peychart/WiFiPowerStrip/C++source/untyped.h

/*           untyped C++ (Version 0.1 - 2012/07)
    <https://github.com/peychart/untyped-cpp>

    Copyright (C) 2012  -  peychart

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
    Details of this licence are available online under:
                        http://www.gnu.org/licenses/gpl-3.0.html
*/
#ifndef HEADER_F2792F1A2356431
#define HEADER_F2792F1A2356431

#include <string>
#include <vector>
#include <map>
#include <iostream>
#include <sstream>
#include <cstdlib>

namespace noType
{
 class untyped : private std::vector<untyped>, private std::map<std::string, untyped>, private std::string
 {  static unsigned short JSON, tabSize;

 protected:
  typedef std::pair<std::string, untyped>  pairType;
  typedef std::vector<untyped>             vectorType;
  typedef std::map<std::string, untyped>   mapType;
  typedef unsigned char                    uchar;
  typedef long                             int64_t;
  typedef unsigned long                    uint64_t;

 public:
  inline static char const* version() {return "0.2";};
  untyped ( void );                   //  0
  untyped ( bool           const   ); //  1
  untyped ( char           const   ); //  2
  untyped ( wchar_t        const   ); //  3
  untyped ( int8_t         const   ); //  4
  untyped ( uint8_t        const   ); //  5
  untyped ( int16_t        const   ); //  6
  untyped ( uint16_t       const   ); //  7
  untyped ( int32_t        const   ); //  8
  untyped ( uint32_t       const   ); //  9
  untyped ( int64_t        const   ); // 10
  untyped ( uint64_t       const   ); // 11
  untyped ( float          const   ); // 12
  untyped ( double         const   ); // 13
  untyped ( char           const * ); // 15
  untyped ( std::string    const & ); // 15
  untyped ( size_t s, void const * ); // 15
  untyped ( pairType       const & ); //  0
  untyped ( vectorType     const & ); //  0
  untyped ( mapType        const & ); //  0
  untyped ( untyped        const & );
  untyped ( std::istream         & );
  virtual ~untyped() {clear();};

  inline size_t                       type        ( void )                const {return (size_t)_type;};
  inline size_t                       size        ( void )                const {return std::string::size();};
  inline size_t                       vectorSize  ( void )                const {return vectorType::size();};
  inline size_t                       mapSize     ( void )                const {return mapType::size();};
  inline bool                         empty       ( void )                const {return( !size() && !vectorSize() && !mapSize() );};

  inline untyped&                     clear       ( void )                      {return clearValue().clearMap().clearVector();};
  inline untyped&                     clearValue  ( void )                      {std::string::clear(); _type=0; return *this;};
  inline untyped&                     clearVector ( void )                      {vectorType::clear(); return *this;};
  inline untyped&                     clearMap    ( void )                      {mapType::clear();    return *this;};
  inline char const *                 data        ( void )                const {return std::string::data();};
  inline char const *                 c_str       ( void )                const {return std::string::c_str();};

  inline std::string&                 string      ( void )                      {return (*((std::string*)this));};
  inline vectorType&                  vector      ( void )                      {return (*((vectorType*)this));};
  inline untyped&                     at          ( size_t i )                  {return vectorType::at(i);};
  inline mapType&                     map         ( void )                      {return (*((mapType*)this));};
  inline untyped&                     at          ( const char s[] )            {return mapType::at(s);};
  inline untyped&                     at          ( std::string s )             {return mapType::at(s);};

  untyped&                            assign      ( untyped const &  );
  template<class T> untyped&          assign      ( T       const &v )          {return assign( untyped( v ) );};
  template<class T> untyped&          assign      ( char    const *v )          {return assign( untyped( v ) );};
  inline untyped&                     assign      ( size_t s, void const *v )   {return assign( untyped( s, v ) );};

  template<typename T> inline T       value       ( T &v )                const {return  v=this->value<T>();};
  template<typename T> inline T*      value       ( T* &p )               const {return  p=reinterpret_cast<T*>(data());};
  template<typename T> inline T const *value      ( T const * &p )        const {return  p=reinterpret_cast<T const *>(data());};
  template<typename T> T              value       ( void )                const {
    switch( _type ) {
      case  1: if( size() ) return( *reinterpret_cast<bool     const *>(data()) ); break;
      case  2: if( size() ) return( *reinterpret_cast<char     const *>(data()) ); break;
      case  3: if( size() ) return( *reinterpret_cast<wchar_t  const *>(data()) ); break;
      case  4: if( size() ) return( *reinterpret_cast<int8_t   const *>(data()) ); break;
      case  5: if( size() ) return( *reinterpret_cast<uint8_t  const *>(data()) ); break;
      case  6: if( size() ) return( *reinterpret_cast<int16_t  const *>(data()) ); break;
      case  7: if( size() ) return( *reinterpret_cast<uint16_t const *>(data()) ); break;
      case  8: if( size() ) return( *reinterpret_cast<int32_t  const *>(data()) ); break;
      case  9: if( size() ) return( *reinterpret_cast<uint32_t const *>(data()) ); break;
      case 10: if( size() ) return( *reinterpret_cast<int64_t  const *>(data()) ); break;
      case 11: if( size() ) return( *reinterpret_cast<uint64_t const *>(data()) ); break;
      case 12: if( size() ) return( *reinterpret_cast<float    const *>(data()) ); break;
      case 13: if( size() ) return( *reinterpret_cast<double   const *>(data()) ); break;
      case 15: return( *data() );
    } return T();
  };

  template<typename T>                operator T  ( void )               const  {return  value<T>();};
  template<typename T>                operator T* ( void )               const  {return  reinterpret_cast<T*>(data());};

  template<class T> untyped&          operator=   ( T const &that )             {return  operator= ( untyped( that ) );};
  inline untyped&                     operator=   ( untyped const &that )       {return  assign(that);};

  template<class T> bool              operator==  ( T const &that )       const {return  operator==( untyped( that ) );};
  bool                                operator==  ( untyped const &that ) const;
  template<class T> bool              operator!=  ( T const &that )       const {return  operator!=( untyped( that ) );};
  inline bool                         operator!=  ( untyped const &that ) const {return !operator==( that );};
  template<class T> bool              operator<   ( T const &that )       const {return  operator< ( untyped( that ) );};
  bool                                operator<   ( untyped const &that ) const;
  template<class T> bool              operator<=  ( T const &that )       const {return  operator<=( untyped( that ) );};
  inline bool                         operator<=  ( untyped const &that ) const {return( operator< ( that ) || operator==( that ) );};
  template<class T> bool              operator>   ( T const &that )       const {return  operator> ( untyped( that ) );};
  inline bool                         operator>   ( untyped const &that ) const {return !operator<=( that );};
  template<class T> bool              operator>=  ( T const &that )       const {return  operator>=( untyped( that ) );};
  inline bool                         operator>=  ( untyped const &that ) const {return !operator< ( that );};

  template<class T> inline untyped&   operator+=  ( T const &that )             {return  operator+=( untyped( that ) );};
  untyped&                            operator+=  ( untyped const & );
  template<class T> inline untyped    operator+   ( T const &that )       const {return  operator+ ( untyped( that ) );};
  inline untyped                      operator+   ( untyped const &that ) const {return  untyped( *this ).operator+=( that );};
  template<class T> inline untyped&   operator-=  ( T const &that )             {return  operator-=( untyped( that ) );};
  untyped&                            operator-=  ( untyped const &  );
  template<class T> inline untyped    operator-   ( T const &that )       const {return  operator- ( untyped( that ) );};
  inline untyped                      operator-   ( untyped const &that ) const {return  untyped( *this ).operator-=( that );};
  template<class T> inline untyped&   operator*=  ( T const &that )             {return  operator*=( untyped( that ) );};
  untyped&                            operator*=  ( untyped const &  );
  template<class T> inline untyped    operator*   ( T const &that )       const {return  operator* ( untyped( that ) );};
  inline untyped                      operator*   ( untyped const &that ) const {return  untyped( *this ).operator*=( that );};
  template<class T> inline untyped&   operator/=  ( T const &that )             {return  operator/=( untyped( that ) );};
  untyped&                            operator/=  ( untyped const &  );
  template<class T> inline untyped    operator/   ( T const &that )       const {return  operator/ ( untyped( that ) );};
  inline untyped                      operator/   ( untyped const &that ) const {return  untyped( *this ).operator/=( that );};
  template<class T> inline untyped&   operator%=  ( T const &that )             {return  operator%=( untyped( that ) );};
  untyped&                            operator%=  ( untyped const &  );
  template<class T> inline untyped    operator%   ( T const &that )       const {return  operator% ( untyped( that ) );};
  inline untyped                      operator%   ( untyped const &that ) const {return  untyped( *this ).operator%=( that );};
  template<class T> inline untyped&   operator&=  ( T const &that )             {return  operator&=( untyped( that ) );};
  untyped&                            operator&=  ( untyped const &  );
  template<class T> inline untyped    operator&   ( T const &that )       const {return  operator& ( untyped( that ) );};
  inline untyped                      operator&   ( untyped const &that ) const {return  untyped( *this ).operator&=( that );};
  template<class T> inline untyped&   operator|=  ( T const &that )             {return  operator|=( untyped( that ) );};
  untyped&                            operator|=  ( untyped const &  );
  template<class T> inline untyped    operator|   ( T const &that )       const {return  operator| ( untyped( that ) );};
  inline untyped                      operator|   ( untyped const &that ) const {return  untyped( *this ).operator|=( that );};

  inline untyped&                     operator[]  ( int n )                     {return operator[](size_t(n));};
  inline untyped&                     operator[]  ( long   n )                  {return operator[](size_t(n));};
  inline untyped&                     operator[]  ( size_t n )                  {while(n >= vectorSize()) vectorType::push_back(untyped()); return at(n);};
  inline untyped&                     operator[]  ( const char s[] )            {return( operator[]( std::string(s) ) );};
  inline untyped&                     operator[]  ( std::string s )             {mapType::iterator it(mapType::find(s)); return( (it!=mapType::end()) ?(it->second) :(mapType::operator[](s)=untyped()) );};

  virtual untyped&                    serialize       ( std::ostream & );
  virtual untyped&                    serializeJson   ( std::ostream &o )       {return serializePrettyJson( o, untyped::tabSize );};
  virtual untyped&                    serializePrettyJson( std::ostream &o, unsigned short v=1 )
                                                                                {unsigned short b(untyped::JSON),t(untyped::tabSize); prettyJson(v); o << *this; if((untyped::JSON=b)) prettyJson(t); return *this;};
  inline std::string                  serializeJson   ( void )                  {std::stringstream o; serializePrettyJson( o, untyped::tabSize ); return o.str();};
  inline std::string                  serializePrettyJson( unsigned short v=1 ) {std::stringstream o; serializePrettyJson( o, v );                return o.str();};

  virtual untyped&                    deserialize     ( std::string  s )        {std::istringstream i(s); return(isBinary() ?deserialize(i) :deserializeJson(i));};
  virtual untyped&                    deserialize     ( std::istream & );
  virtual untyped&                    deserializeJson ( std::string  s )        {std::istringstream i(s); return deserializeJson(i);};
  virtual untyped&                    deserializeJson ( std::istream & );
  inline untyped&                     operator()      ( std::string  s )        {std::istringstream i(s); return operator()(i);};
  inline untyped&                     operator()      ( std::istream &i )       {return deserialize(i);};

  friend std::ostream&                operator<<      ( std::ostream &, untyped const & );
  friend std::ostream&                operator<<      ( std::ostream &, mapType const & );
  friend std::ostream&                operator<<      ( std::ostream &, vectorType const & );
  friend std::ostream&                operator<<      ( std::ostream &out, pairType const &that ) {return out << that.first << ": " << that.second;};

  inline bool                         isBinary        ( void )            const {return( !untyped::JSON );};
  inline bool                         isJson          ( void )            const {return(  untyped::JSON );};
  inline bool                         isPrettyJson    ( void )            const {return(  untyped::tabSize );};
  inline untyped&                     binary          ( void )                  {untyped::JSON=untyped::tabSize=0; return *this;};
  inline untyped&                     json            ( void )                  {return prettyJson(0);};
  inline untyped&                     prettyJson      ( short v=1 )             {untyped::JSON=1; untyped::tabSize=(v<0 ?0 :v); return *this;};

 protected:
  static bool                         isNetFormat     ( void )                  {short isNotNet=1; return( !*reinterpret_cast<char const *>(&isNotNet) );};
  template<typename T> static char const *hton        ( T val )                 {
    static T tmp; tmp=val; ntoh( reinterpret_cast<char*>(&tmp), sizeof(T) );
    return( reinterpret_cast<char const *>(&tmp) );
  };  // Net to Host format...
  inline void                         ntoh            ( std::string& p )        {
    if (p.size() && !isNetFormat() )
      for(size_t i(0), j(p.size()-1); i<j; i++, j--)
        std::swap( p[i], p[j] );
  };
  template<typename T> static inline void ntoh        ( T *p, size_t const size ){
    if (p && !isNetFormat())
      for( char *pt1=reinterpret_cast<char*>(p),*pt2 = pt1+size-1; pt1<pt2; pt1++,pt2-- )
        std::swap( *pt1, *pt2 );
  };

  static inline size_t        stringSize      ( char const *v )                 {size_t s(0); if (v) while( *v++ ) s++; return s;};

 private:
  uchar                       _type; /// WARNING: type must be < 32 [5+3 bits shared with desc(structure) in a char for the serialization methods...]

  inline void                 _set            ( size_t l,char const* v )        {std::string::assign(v, l);};
  inline void                 _set            ( vectorType   const &v )         {for(size_t i(0); i<v.size(); i++) operator[](vectorSize())= v[i];};
  inline void                 _set            ( mapType      const &v )         {for(mapType::const_iterator it=v.begin(); it!=v.end(); it++) operator[](it->first)= it->second;};
  static void                 _writeTypeAndStructure( std::ostream&, uchar, uchar const & );
  static inline void          _writeSize      ( std::ostream& o, size_t s )     {o.write( hton(s), sizeof(s) );};
  static uchar                _readTypeAndStructure ( std::istream&, uchar & );
  static inline void          _readSize       ( std::istream &in, size_t &s )   {if( in.read(reinterpret_cast<char*>(&s), sizeof(s)) ) ntoh( &s, sizeof(s) );};

  static untyped              _getJsonObject  ( std::istream &, char &, bool=false );
  static untyped              _getJsonArray   ( std::istream &, char &, bool=false );
  static untyped              _getJsonValue   ( std::istream &, char &, char='\0' );
  static untyped              _getJsonString  ( std::istream &, char & );
  static untyped              _getJsonChar    ( std::istream &, char & );
  static untyped              _getJsonNumber  ( std::istream &, char & );
  static untyped              _getJsonBool    ( std::istream &, char & );
  static void                 _getJsonNull    ( std::istream &, char & );
  static void                 _getJsonComment ( std::istream &, char & );
  static inline void          _jsonTAB        ( std::ostream &o )               {if(untyped::JSON) for(unsigned short i(untyped::JSON-1); i; i--) o.write(" ", 1);};
  static inline void          _jsonNL         ( std::ostream &o )               {if(untyped::tabSize) o.write("\n", 1);};
  static inline void          _jsonSP         ( std::ostream &o )               {if(untyped::tabSize) o.write(" ", 1);};
  static inline void          _jsonINCR       ( void )                          {if(untyped::JSON) untyped::JSON+=untyped::tabSize;};
  static inline void          _jsonDECR       ( void )                          {if(untyped::JSON>untyped::tabSize) untyped::JSON-=untyped::tabSize;};

  static inline bool          _isWhiteSpace   ( char &c )                       {if(c==' ' || c=='\t' || c=='\r' || c=='\n') return true; return false;};
 };
}
using namespace noType;
#endif
