peychart/WiFiPowerStrip/C++source/mqtt.h

/* ESP8266-MQTT-Manager C++ (Version 0.1 - 2020/07)
    <https://github.com/peychart/WiFiPowerStrip>

    Copyright (C) 2020  -  peychart

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
    Details of this licence are available online under:
                        http://www.gnu.org/licenses/gpl-3.0.html
*/
// https://diyi0t.com/microcontroller-to-raspberry-pi-wifi-mqtt-communication/
// https://pubsubclient.knolleary.net/api.html
// https://links2004.github.io/Arduino/dc/da7/class_wi_fi_client.html
#ifndef HEADER_FB324C732446218
#define HEADER_FB324C732446218

#include <Arduino.h>
#include <ESP8266WiFi.h>
#include <WiFiClient.h>
#include <PubSubClient.h>
#include <LittleFS.h>
#include "untyped.h"

#include "setting.h"
#include "debug.h"

// Json name attributes:
#ifndef ROUTE_MQTT_BROKER
  #define ROUTE_MQTT_BROKER  "mqttBroker"
  #define ROUTE_MQTT_PORT    "mqttPort"
  #define ROUTE_MQTT_IDENT   "mqttIdent"
  #define ROUTE_MQTT_USER    "mqttUser"
  #define ROUTE_MQTT_PWD     "mqttPwd"
  #define ROUTE_MQTT_PUBTOPIC "mqttOuTopic"
#endif

#ifndef G
  #define G(n)                String(F(n)).c_str()
#endif

namespace MQTT {
 class mqtt : public PubSubClient, public untyped {
  public:
    mqtt ( void );

    virtual ~mqtt()          {saveToSD();};

    inline mqtt&              broker         ( std::string v )  {_changed|=(at(G(ROUTE_MQTT_BROKER))   !=v); at(G(ROUTE_MQTT_BROKER))  = v; return *this;};
    inline bool               disabled       ( void )           {return broker().empty();};
    inline mqtt&              port           ( short v )        {_changed|=(at(G(ROUTE_MQTT_PORT))     !=v); at(G(ROUTE_MQTT_PORT))    = v; return *this;};
    inline mqtt&              ident          ( std::string v )  {_changed|=(at(G(ROUTE_MQTT_IDENT))    !=v); at(G(ROUTE_MQTT_IDENT))   = v; return *this;};
    inline mqtt&              user           ( std::string v )  {_changed|=(at(G(ROUTE_MQTT_USER))     !=v); at(G(ROUTE_MQTT_USER))    = v; return *this;};
    inline mqtt&              password       ( std::string v )  {_changed|=(at(G(ROUTE_MQTT_PWD))      !=v); at(G(ROUTE_MQTT_PWD))     = v; return *this;};
    inline mqtt&              pubTopic       ( std::string v )  {_changed|=(at(G(ROUTE_MQTT_PUBTOPIC)) !=v); at(G(ROUTE_MQTT_PUBTOPIC)) = v; return *this;};
    inline std::string        broker         ( void )           {return at(G(ROUTE_MQTT_BROKER)  ).c_str();};
    inline short              port           ( void )           {return at(G(ROUTE_MQTT_PORT)    );};
    inline std::string        ident          ( void )           {return at(G(ROUTE_MQTT_IDENT)   ).c_str();};
    inline std::string        user           ( void )           {return at(G(ROUTE_MQTT_USER)    ).c_str();};
    inline std::string        password       ( void )           {return at(G(ROUTE_MQTT_PWD)     ).c_str();};
    inline std::string        pubTopic       ( void )           {return at(G(ROUTE_MQTT_PUBTOPIC) ).c_str();};
    inline bool               changed        ( void )           {return _changed;};
    inline mqtt&              changed        ( bool force )     {_changed=force; return *this;};
    void                      loop           ( void );
    inline mqtt&              subscribe      ( std::string s )  {_subscribeTopic.push_back(s); return *this;};
    inline
    std::vector<std::string>& subscribe      ( void )           {return _subscribeTopic;};

    bool                      reconnect      ( void );
    bool                      send           ( std::string, std::string = "", bool = false );
    static void               callback       ( char*, byte*, unsigned int );

    mqtt&                     set            ( untyped );
    bool                      saveToSD       ( void );
    bool                      restoreFromSD  ( void );

  private:
    bool                      _changed;
    WiFiClient                _ethClient;
    std::vector<std::string>  _subscribeTopic;

    inline static bool        _isInMqtt      ( std::string s )  {return(
          s==G(ROUTE_MQTT_BROKER)
      ||  s==G(ROUTE_MQTT_PORT)
      ||  s==G(ROUTE_MQTT_IDENT)
      ||  s==G(ROUTE_MQTT_USER)
      ||  s==G(ROUTE_MQTT_PWD)
      ||  s==G(ROUTE_MQTT_PUBTOPIC)
    );};
 };
}
using namespace MQTT;

#endif
