peychart/WiFiPowerStrip/C++source/mqtt.cpp

/* ESP8266-MQTT-Manager C++ (Version 0.1 - 2020/07)
    <https://github.com/peychart/WiFiPowerStrip>

    Copyright (C) 2020  -  peychart

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
    Details of this licence are available online under:
                        http://www.gnu.org/licenses/gpl-3.0.html
*/
#include "mqtt.h"

namespace MQTT
{
  mqtt::mqtt( void ) : _changed(false) {
    setClient( _ethClient );
    operator[](G(ROUTE_MQTT_BROKER))   = "";
    operator[](G(ROUTE_MQTT_PORT))     = 1883;
    operator[](G(ROUTE_MQTT_IDENT))    = "";
    operator[](G(ROUTE_MQTT_USER))     = "";
    operator[](G(ROUTE_MQTT_PWD))      = "";
    operator[](G(ROUTE_MQTT_PUBTOPIC)) = "";
    json();
  }

  bool mqtt::reconnect() {
    if( !this->connected() ){
      this->setServer( broker().c_str(), port() );
      if( (!_ethClient.connected() && !_ethClient.connect(broker().c_str(), port()))
        || !this->connect( ident().c_str(), user().c_str(), password().c_str() ) )
        return false;
      DEBUG_print(F("Connected to MQTT broker: \"")); DEBUG_print(broker().c_str()); DEBUG_print(F("\".\n"));
      for(auto x :_subscribeTopic){
        DEBUG_print("Subcribe to: "); DEBUG_print(x.c_str()); DEBUG_print("\n");
        PubSubClient::subscribe( x.c_str() );
      }
    }return true;
  }

  void mqtt::loop( void ) {
    static ulong last(0L);
    if( !disabled() ){
      ulong now(millis());
      PubSubClient::loop();
      if( now-last > 5000 ){
        reconnect(); last=now;
  } } }

  bool mqtt::send( std::string s, std::string topic, bool retain ) {
    if( !disabled() && reconnect() ){
      topic = pubTopic() + (((!pubTopic().length() || pubTopic()[pubTopic().length()-1]!='/') && topic.length()) ?"/" :"") + topic;
      if( topic.length() && topic[topic.length()-1]=='/' ) topic = topic.substr(0, topic.length()-1);
      if( !this->beginPublish(topic.c_str(), s.size(), true ) ){
        DEBUG_print(F("Cannot write to MQTT broker: \"")); DEBUG_print(broker().c_str());
        DEBUG_print(F("\" on topic \"")); DEBUG_print(topic.c_str());
        DEBUG_print(F(".\n"));
        return false;
      }uint8_t c; for(ulong i(0); (i+=write(&(c=s[i]),1)) < s.size(); ); this->endPublish();
      DEBUG_print(F("Received: \"")); DEBUG_print(s.c_str()); DEBUG_print(F("\" published to \"")); DEBUG_print(broker().c_str());
      DEBUG_print(F("\" on topic \"")); DEBUG_print(topic.c_str()); DEBUG_print(F("\".\n"));
    }return true;
  }

  mqtt& mqtt::set( untyped v ) {
    bool modified(false);
    for(auto &x :v.map()) if(_isInMqtt( x.first ) ){
      modified|=( at( x.first ) != x.second );
      this->operator+=( x );
    }return changed( modified );
  }

  bool mqtt::saveToSD(){
    if( !_changed ) return true;
    if( LittleFS.begin() ) {
      File file( LittleFS.open( F("/mqtt.cfg"), "w" ) );
      if( file ) {
            _changed = !file.println( this->serializeJson().c_str() );
            file.close();
            DEBUG_print(F("mqtt.cfg writed.\n"));
      }else{DEBUG_print(F("Cannot write mqtt.cfg !...\n"));}
      LittleFS.end();
    }else{DEBUG_print(F("Cannot open SD!...\n"));}
    return !_changed;
  }

  bool mqtt::restoreFromSD(){
    if( LittleFS.begin() ) {
      File file( LittleFS.open( F("/mqtt.cfg"), "r" ) );
      if( file ) {
            _changed = this->deserializeJson( file.readStringUntil('\n').c_str() ).empty();
            file.close();
            DEBUG_print(F("mqtt.cfg restored.\n"));
      }else{DEBUG_print(F("Cannot read mqtt.cfg !...\n"));}
      LittleFS.end();
    }else{DEBUG_print(F("Cannot open SD!...\n"));}
    return !_changed;
  }

}
