peychart/WiFiPowerStrip/C++source/switches.cpp

/* ESP8266-Switches-Manager C++ (Version 0.1 - 2020/07)
    <https://github.com/peychart/WiFiPowerStrip>

    Copyright (C) 2020  -  peychart

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
    Details of this licence are available online under:
                        http://www.gnu.org/licenses/gpl-3.0.html
*/
#include "switches.h"

namespace Switches
{
  void switches::inputEvent( volatile bool& intr, volatile ulong& rebound_completed ) {
    if( intr && (intr =_interruptTraitement) ) {
      if(_isNow( rebound_completed ) ){     //Rebound completed
        if( !_in_post_rebound ){            //switch is now activated...
          (this->*_interruptTraitement)();  //intr = _pushCount;
           rebound_completed = millis() + POST_DEBOUNCE_TIME;
           _in_post_rebound = !_pushCount;
        }else intr = _in_post_rebound = false;
  } } }

  ushort switches::_getInputs(uint16_t reg){
    ushort i(0), n(0);
    for(auto x : *this){
      if( (reg & (1<<x.gpio())) == (x.mode()==INPUT) )
        n += (1<<i);
      i++;
    }return n;
  }

  void switches::_treatment_1() {                //<-- Switches.size() <= _outPins.size():
    ushort n(_getInputs(GPI) );
    if( !_pushCount ){
      _pushCount=n;
      _next_timerDisabler = millis() + HOLD_TO_DISABLE_TIMER * 1000UL;
      DEBUG_print(F("\nIO init: ")); for(ushort i(size()); i; i--) DEBUG_print(n&(1<<(i-1)) ?1 :0); DEBUG_print(F("\n"));
    }else if( !n ){
      if( --_pushCount < _outPins.size() ){
        if(_isNow(_next_timerDisabler ) ){
          if(_outPins[_pushCount ].isOff() )
            _outPins[_pushCount ].set(_outPins[_pushCount ].isOff() );   //<-- set output
          _outPins[_pushCount ].stopTimer();
          DEBUG_print(F("Timer removed on ")); DEBUG_print(String(operator()(n).gpio(),DEC)); DEBUG_print(F("(")); DEBUG_print(_outPins[n].name().c_str()); DEBUG_print(F(")")); DEBUG_print(F("\n"));
        }else _outPins[_pushCount ].set(_outPins[_pushCount ].isOff() );  //<-- switch output
        _pushCount=0;
  } } }

  void switches::_treatment_2() {                //<-- single-switch multi-outputs:
    static bool lock(false);
    ushort n(_getInputs(GPI) );
    if ( n && !lock ){ // switch activation.
      _next_timerDisabler = millis() + HOLD_TO_DISABLE_TIMER * 1000UL;
      _cmd_completed      = millis() + CMD_COMPLETED_TIMER   * 1000UL;
      _pushCount++; lock=true;
      DEBUG_print(F("\nIO init: ")); for(ushort i(size()); i; i--) DEBUG_print(n&(1<<(i-1)) ?1 :0); DEBUG_print(F("\n"));
    }else if(_isNow(_cmd_completed ) || _isNow(_next_timerDisabler ) ){
      if( --_pushCount < _outPins.size() ){
        _outPins[_pushCount ].set( _outPins[_pushCount ].isOff() );    //<-- (un)set output
        if( n && _isNow(_next_timerDisabler ) ){ //<-- Unset output timer
          _outPins(_pushCount ).stopTimer();
          DEBUG_print(F("Timer removed on ")); DEBUG_print(String(operator()(n).gpio(),DEC)); DEBUG_print(F("(")); DEBUG_print(_outPins[n].name().c_str()); DEBUG_print(F(")")); DEBUG_print(F("\n"));
        }lock=(_pushCount=0);
    } }
    else if( !n )
      lock=(_pushCount=0);
  }

}
