peychart/WiFiPowerStrip/C++source/ntp.h

/* ESP8266-NTP-Manager C++ (Version 0.1 - 2020/07)
    <https://github.com/peychart/WiFiPowerStrip>

    Copyright (C) 2020  -  peychart

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
    Details of this licence are available online under:
                        http://www.gnu.org/licenses/gpl-3.0.html
*/
#ifndef HEADER_EC332E292901801
#define HEADER_EC332E292901801

#include <Arduino.h>
#include <WiFiClient.h>
#include <NtpClientLib.h>
#include <LittleFS.h>
#include "untyped.h"

#include "setting.h"
#include "debug.h"

// Json name attributes:
#ifndef ROUTE_NTP_SOURCE
  #define ROUTE_NTP_SOURCE    "ntpSource"
  #define ROUTE_NTP_ZONE      "ntpZone"
  #define ROUTE_NTP_DAYLIGHT  "ntpDayLight"
#endif
#define ROUTE_NTP_INTERVAL    "ntpInterval"
#define ROUTE_NTP_DISABLED    "ntpDisabled"
#ifndef G
  #define G(n)                 String(F(n)).c_str()
#endif

namespace _NTP {
 class ntp : public untyped {
  public:
    ntp ( void );

    virtual ~ntp()     {saveToSD();};

    inline ntp&         disabled       ( bool v )         {_changed|=(at(G(ROUTE_NTP_DISABLED))!= v); at(G(ROUTE_NTP_DISABLED)) = v; this->begin(); return *this;};
    inline ntp&         source         ( std::string v )  {_changed|=(at(G(ROUTE_NTP_SOURCE))  != v); at(G(ROUTE_NTP_SOURCE))   = v; return *this;};
    inline ntp&         zone           ( short v )        {_changed|=(at(G(ROUTE_NTP_ZONE))    != v); at(G(ROUTE_NTP_ZONE))     = v; return *this;};
    inline ntp&         dayLight       ( bool v )         {_changed|=(at(G(ROUTE_NTP_DAYLIGHT))!= v); at(G(ROUTE_NTP_DAYLIGHT)) = v; return *this;};
    inline ntp&         interval       ( ulong v )        {_changed|=(at(G(ROUTE_NTP_INTERVAL))!= v); at(G(ROUTE_NTP_INTERVAL)) = v; return *this;};
    inline bool         disabled       ( void )           {return !source().empty() && at(G(ROUTE_NTP_DISABLED));};
    inline std::string  source         ( void )           {return at(G(ROUTE_NTP_SOURCE)  ).c_str();};
    inline short        zone           ( void )           {return at(G(ROUTE_NTP_ZONE)    );};
    inline bool         dayLight       ( void )           {return at(G(ROUTE_NTP_DAYLIGHT));};
    inline ulong        interval       ( void )           {return at(G(ROUTE_NTP_INTERVAL));};
    inline bool         changed        ( void )           {return _changed;};
    inline ntp&         changed        ( bool force )     {_changed=force; return *this;};

    void                begin          ( void );
    inline bool         isSynchronized ( ulong t=now() )  {return( t>-1UL/10UL );};
    inline void         getTime        ( void )           {if( !source().empty() && !isSynchronized() ) {DEBUG_print(F("Retry NTP synchro...\n")); NTP.getTime();};};

    ntp&                set            ( untyped );
    bool                saveToSD       ( void );
    bool                restoreFromSD  ( void );

  private:
    bool                _changed;
    
    inline static bool  _isInNTP       ( std::string s )  {return(
          s==G(ROUTE_NTP_SOURCE)
      ||  s==G(ROUTE_NTP_ZONE)
      ||  s==G(ROUTE_NTP_DAYLIGHT)
      ||  s==G(ROUTE_NTP_INTERVAL)
      ||  s==G(ROUTE_NTP_DISABLED)
    );};
 };
}
using namespace _NTP;

#endif
